SP5GW/RF_VLF_SAQ_Reception/img/antenna_comparison/loop 2025-12-31 171257.png

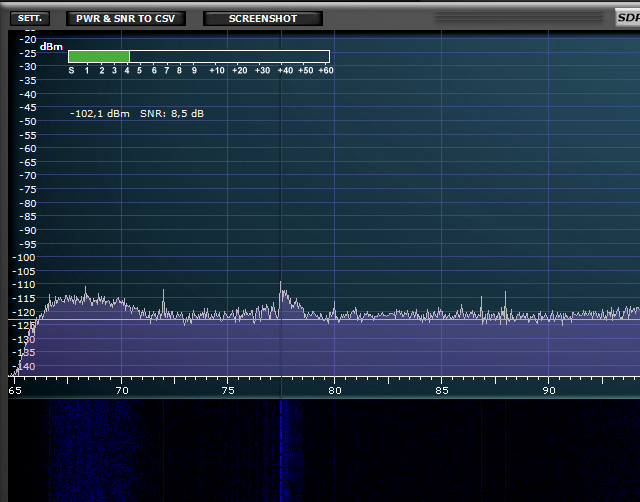
img/antenna_comparison/loop 2025-12-31 171257.png
