SP5GW/RF_VLF_SAQ_Reception/img/antenna_comparison/loop_vlf 2025-12-31 171412.png

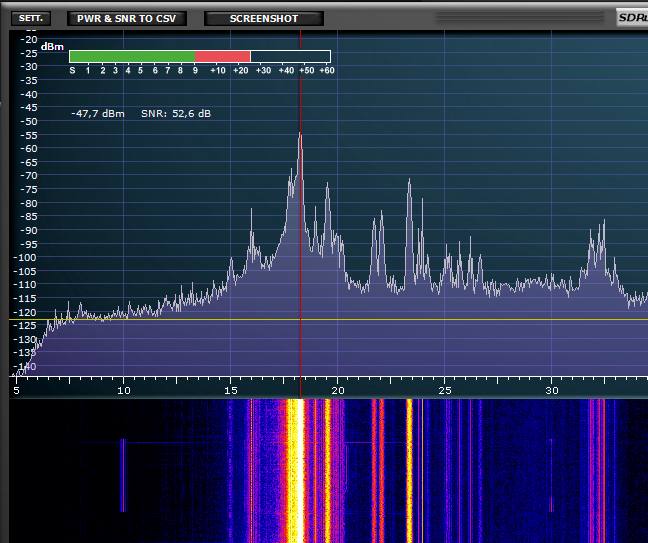
img/antenna_comparison/loop_vlf 2025-12-31 171412.png
