SP5GW/RF_VLF_SAQ_Reception/img/antenna_comparison/miniwhip_225khz 2025-12-31 171257.png

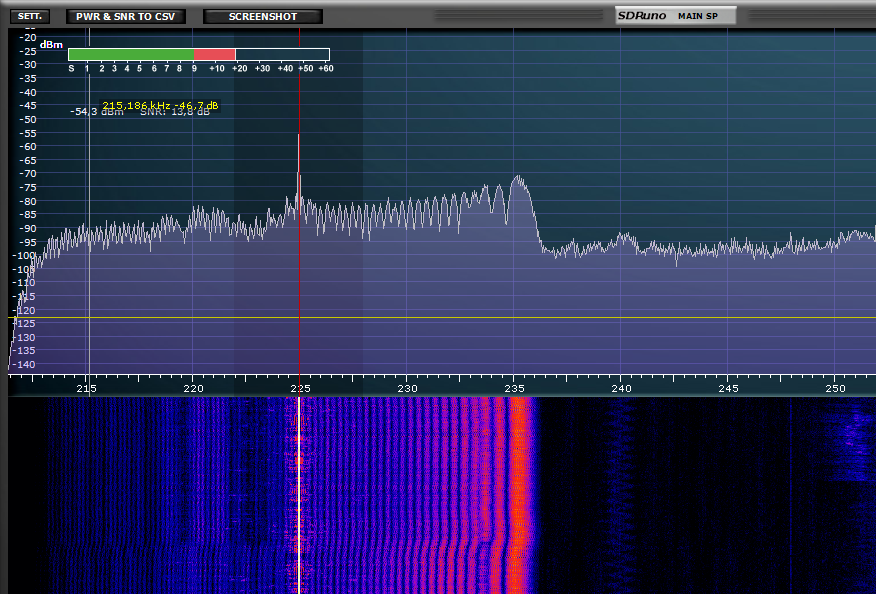
img/antenna_comparison/miniwhip_225khz 2025-12-31 171257.png
