SP5GW/RF_VLF_SAQ_Reception/img/antenna_positioning/azimuth.png

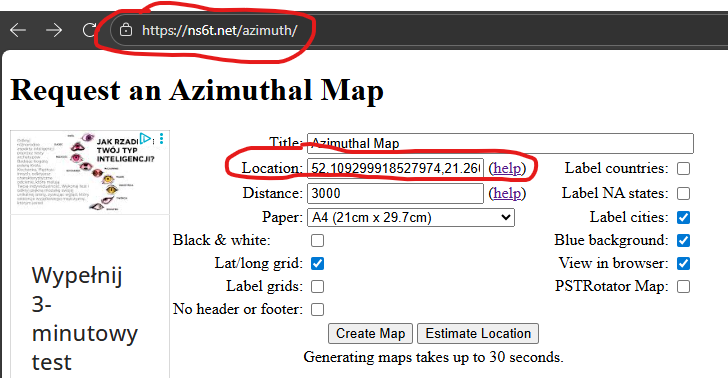
img/antenna_positioning/azimuth.png
