SP5GW/RF_VLF_SAQ_Reception/meas/RealSignals_plus_pilot17kHz2_Decimation32_2n2_SDR_Uno.png

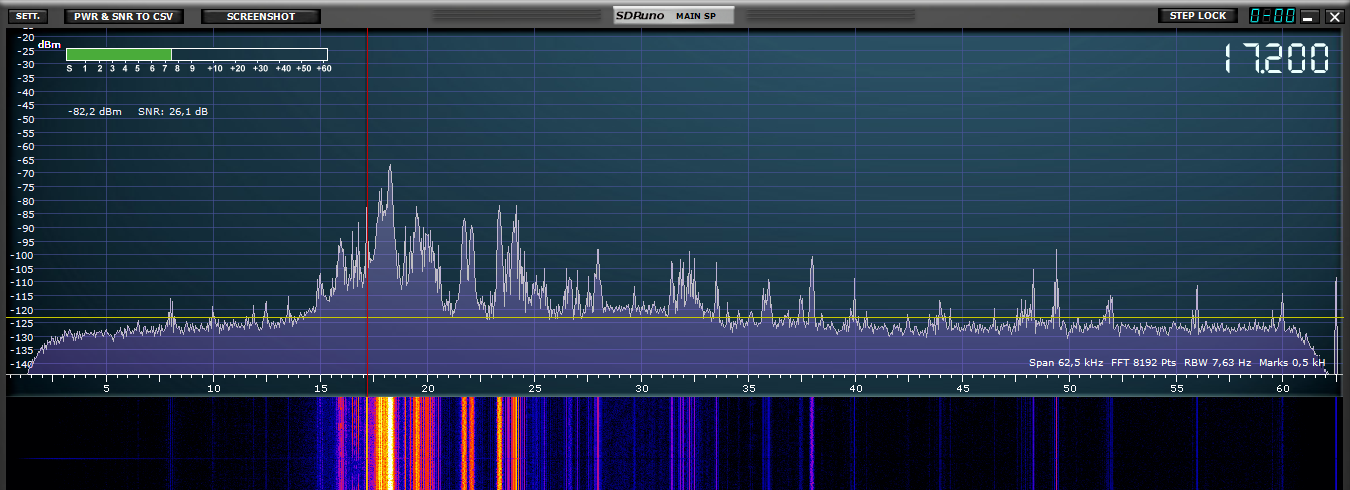
meas/RealSignals_plus_pilot17kHz2_Decimation32_2n2_SDR_Uno.png
