SP5GW/RF_VLF_SAQ_Reception/meas/RealSignals_plus_pilot17kHz2_Decimation32_34_2nF_SDR_Uno.png

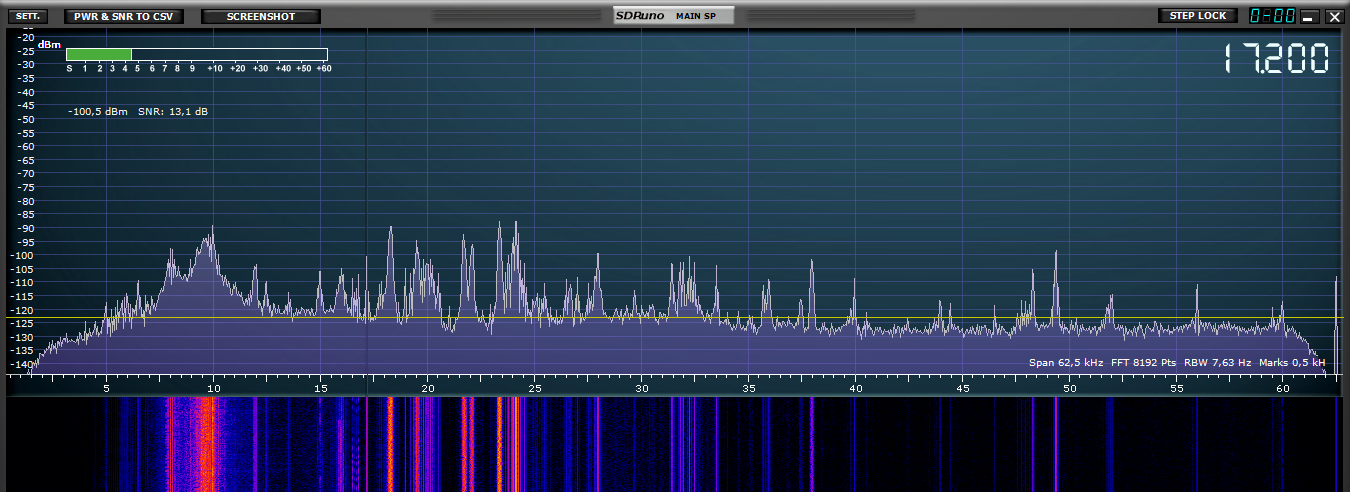
meas/RealSignals_plus_pilot17kHz2_Decimation32_34_2nF_SDR_Uno.png
