SP5GW/RF_VLF_SAQ_Reception/meas/saqrx_antenna_disconnected.png

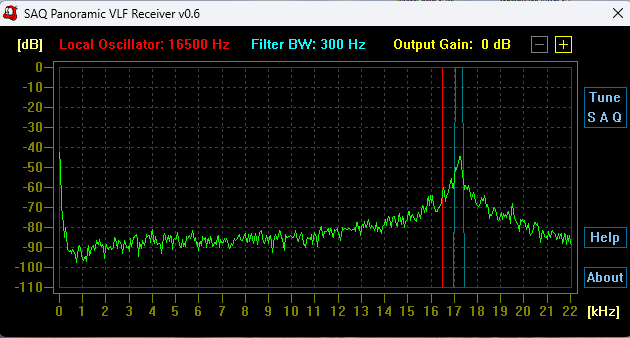
meas/saqrx_antenna_disconnected.png
