SP5GW/RF_VLF_SAQ_Reception/meas/Voltage_In_Out_CenterFreq.png

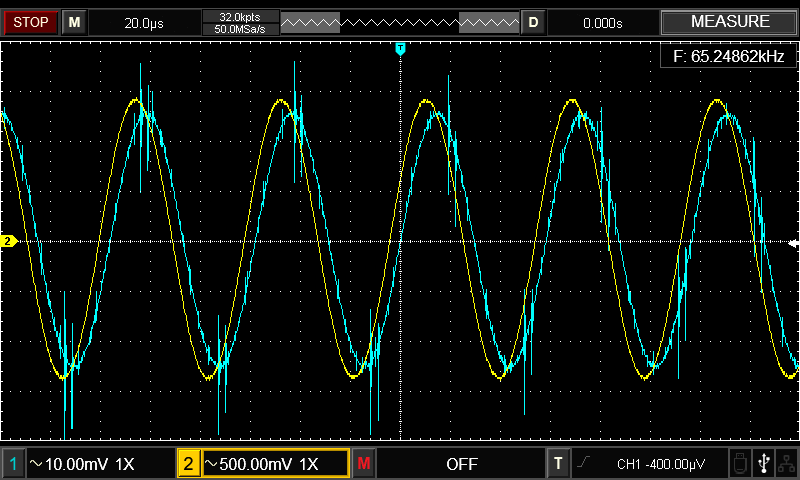
meas/Voltage_In_Out_CenterFreq.png
