SP5GW/RF_VLF_SAQ_Reception/meas/Voltage_In_Out_CenterFreq_2.png

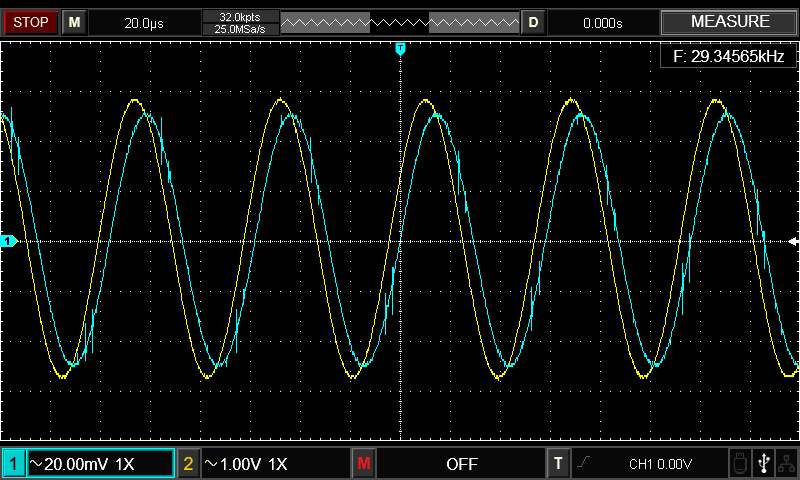
meas/Voltage_In_Out_CenterFreq_2.png
