SP5GW/RF_VLF_SAQ_Reception/sim/SAQ_Receiver.asc

C1: cap; 100n
C2: cap; 1n
C3: cap; 8n2
C4: cap; 1n
C5: cap; 100n
C6: cap; 22n
D1: schottky; 1N5817
D2: schottky; 1N5817
L1: ind2; 10.35m
L2: ind2; 2.47m
R1: res; 1k
R2: res; 6k8
R3: res; 4.7
R4: res; {r4val}
R5: res; 6k8
R6: res; 1k
R7: res; 50
U1: opamp2; AD8397
U2: opamp2; AD8397
V1: voltage; 9V
V2: voltage; 9V
V3: signal; SINE(0 1m 17.2K); AC 5m
Named nets: 0, stage1_out, Stage2out, GenOut
* AD8397 SPICE Macro-model        
* Description: Amplifier
* Generic Desc: Dual High Current OP Amplifier
* Developed by:
* Revision History: 08/10/2012 - Updated to new header style
* 
* Copyright 2012 by Analog Devices, Inc.
*
* Refer to http://www.analog.com/Analog_Root/static/techSupport/designTools/spiceModels/license/spice_general.html for License Statement. Use of this model 
* indicates your acceptance of the terms and provisions in the License Statement.
* 
* BEGIN Notes:
*
* Not Modeled:
*    
* Parameters modeled include: 
*
* END Notes:
*
* Node assignments
*                                +IN             -IN             Vcc             Vee             Out                             
.subckt AD8397  1               2               99              50              4                               
                                                                                                                
***Differential Stage                                                                                                           
Q1              13              12              14              npn                                             
Q2              17              2               16              npn                                             
Rc1             98              13              Rideal          4.200E+00                                       
Rc2             98              17              Rideal          4.200E+00                                       
Re1             14              15              Rideal          4.148E+00                                       
Re2             15              16              Rideal          4.148E+00                                       
Ibias           15              51              1.00E+00                                                        
Dcmlim1         18              15              DQUIET                                                          
Vcmlim1         18              51              1.526                                                           
                                                                                                                
***Voltage Noise Generation                                                                                                     
HVnoise         12              7               Vvnoise         1                                               
VVnoise         501             0               0                                                               
DVnoise         501             0               Dvnoise                                                         
RVnoise         501             0               0.000817778                                                     
                                                                                                                
***Current Noise Generation on +IN                                                                                                              
FInoise1        12              0               VInoise1        1                                               
VInoise1        502             0               0                                                               
DInoise1        502             0               DInoise1                                                        
RInoise1        502             0               7360                                                            
                                                                                                                
***Current Noise Generation on -IN                                                                                                              
FInoise2        2               0               VInoise2        1                                               
VInoise2        503             0               0                                                               
DInoise2        503             0               DInoise2                                                        
RInoise2        503             0               7360                                                            
 
***Common Mode Injection                                                                                        
Rcm1            1               601             Rideal          100Meg                          
Rcm2            2               601             Rideal          100Meg                          
Gcmr            0               602             601             75              1.00E-06        
Rcmr1           602             603             Rideal          1Meg                            
Rcmr2           603             604             Rideal          1.585E+01                       
Lcmr            604             0               2.522E-03                                       
Ecmr            10              9               603             0               1.000E+00       
 
***Positive Power Supply Rejection                                                                                              
Epsr1           700             0               98              0               1               
Rpsr1           700             701             Rideal          1.00E+02                        
Rpsr2           701             702             Rideal          5.012E-03                       
Lpsr1           702             0               7.977E-07                                       
Epsr2           11              10              701             0               1               
 
***Negative Power Supply Rejection                                                                              
Epsr3           703             0               51              0               1
Rpsr3           703             704             Rideal          1.00E+02        
Rpsr4           704             705             Rideal          5.012E-03       
Lpsr2           705             0               7.977E-07                       
Epsr4           12              11              704             0               1
 
***Input Offset and Bias                                                                        
Vos             1               7               1.000E-03                       
Ios             1               2               2.500E-08                       
 
***Input Impedance                                                                              
Cinv            2               0               1.40E-12                        
Cninv           1               0               1.40E-12                        
 
***1st Gain and Slew limiting                                                                   
Gslew           0               101             17              13              1.0000E+00      
Rslew           101             0               Rideal          2.50E+02                        
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
 
***Supply current correction                                                                                                    
Iq              99              50              0.0055                                                          
Fsup1           99              0               Voutmon         1                                               
*DZsup1         0               802             DZENER2                                                         
*Dsup1          99              802             DQUIET                                                          
Fsup2           0               50              Voutmon         -1                                              
*DZsup2         804             0               DZENER2                                                         
*Dsup2          804             50              DQUIET                                                          
 
                                                                                                                
                                                                                                                
                                                                                                                
                                                                                                                
                                                                                                                
                                                                                                                
                                                                                                                
                                                                                                                
                                                                                                                
                                                                                                                
 
***models                                                                                                       
.model          Rideal          res             T_ABS=-273                                                      
.model          Rnoise          res             T_ABS=27                                                        
.model          npn             npn             BF= 384614.384615385                                                            
.model          dquiet          d                                                                               
.model          dvnoise         d               KF=6075000                                                      
.model          dinoise1        d               KF=0.225                                                        
.model          dinoise2        d               KF=0.225
.model          dzener          d               BV=43.5423175545689
.model          dzener2         d               BV=50
                                                
.ends                                           
*$
.tran 20m
K1 L1 L2 0.855
.ac dec 1000 5k 50k
.step param k list 0.5 0.6 0.9
.step param c5val list 100n 1u
.step param r4val list 50 100050
