SP5GW/RF_VLF_SAQ_Reception/sim/SAQ_LC.asc

C1: cap; 8.2n
L1: ind2; 10.48m
R1: res; 100k
R3: res; {R3val}
V3: signal; SINE(0 1m 17.2K); AC 1m; Rser=50
Named nets: 0
.tran 20m
.ac dec 1k 1k 100k
.step param R3val list 1.5k 50k 100k
