SP5GW/RF_VLF_SAQ_Reception/sim/SAQ_transformer.asc

C1: cap; 26.4n
L1: ind2; 10.48m
L2: ind2; 2.47m
R1: res; 1Meg
R2: res; 50
V3: signal; SINE(0 1m 17.2K); AC 1m
Named nets: 0
.tran 20m
K1 L1 L2 0.87
.ac dec 1k 1k 100k
.step param k list 0.6 0.8
