SP5GW/RF_VLF_SAQ_Reception/img/saq_preamp.kicad_sch

## KiCad design img/saq_preamp.kicad_sch (2025-12-28)

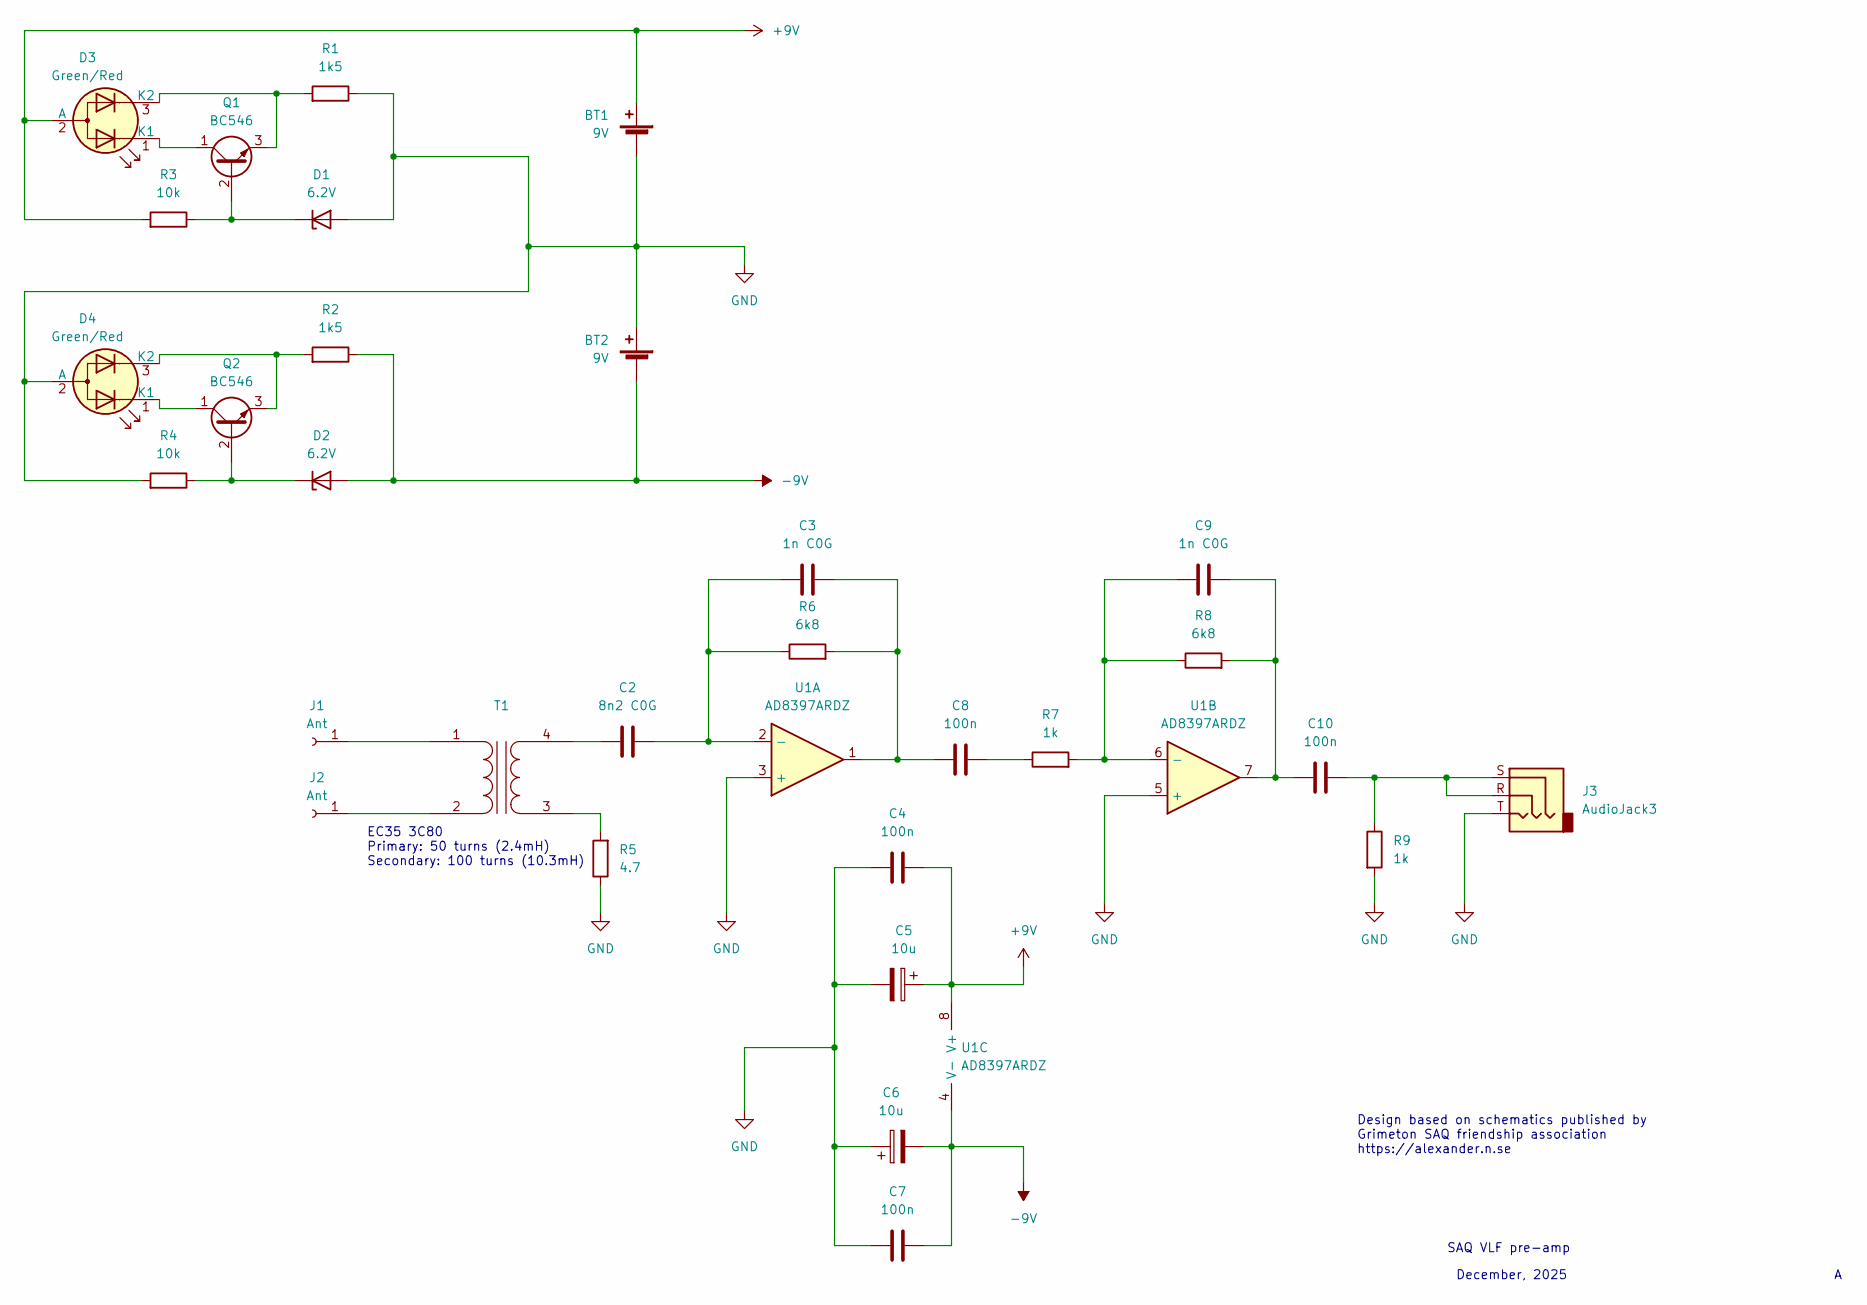
[picture p37: schematic saq_preamp.kicad_sch]

Parts:
BT1, BT2: 9V
C2: 8n2 C0G
C3, C9: 1n C0G
C4, C7, C8, C10: 100n
C5, C6: 10u
D1, D2: 6.2V
D3, D4: Green/Red
J1, J2: Ant
J3: AudioJack3
Q1, Q2: BC546; TO-92_Inline
R1, R2: 1k5
R3, R4: 10k
R5: 4.7
R6, R8: 6k8
R7, R9: 1k
T1: (no value)
U1: AD8397ARDZ

Connections:
+9V: BT1.1 (+), C4.2, C5.1, D3.2 (A), R3.2, U1.8 (V+)
-9V: BT2.2 (-), C6.2, C7.2, D2.2 (A), R2.1, U1.4 (V-)
GND: BT1.2 (-), BT2.1 (+), C4.1, C5.2, C6.1, C7.1, D1.2 (A), D4.2 (A), J3.T, R1.1, R4.2, R5.1, R9.2, U1.3 (+), U1.5 (+)
unnamed: C2.1, T1.4 (SB)
unnamed: C2.2, C3.1, R6.1, U1.2 (-)
unnamed: C3.2, C8.1, R6.2, U1.1
unnamed: C8.2, R7.1
unnamed: C9.1, R7.2, R8.1, U1.6 (-)
unnamed: C9.2, C10.1, R8.2, U1.7
unnamed: C10.2, J3.R, J3.S, R9.1
unnamed: D1.1 (K), Q1.2 (B), R3.1
unnamed: D2.1 (K), Q2.2 (B), R4.1
unnamed: D3.1 (K1), Q1.1 (C)
unnamed: D3.3 (K2), Q1.3 (E), R1.2
unnamed: D4.1 (K1), Q2.1 (C)
unnamed: D4.3 (K2), Q2.3 (E), R2.2
unnamed: J1.1, T1.1 (AA)
unnamed: J2.1, T1.2 (AB)
unnamed: R5.2, T1.3 (SA)

Notes on the sheet:
EC35 3C80 Primary: 50 turns (2.4mH) Secondary: 100 turns (10.3mH)
Design based on schematics published by Grimeton SAQ friendship association https://alexander.n.se
SAQ VLF pre-amp
December, 2025
